Elecrow-RD/CrowPanel-ESP32-3.7-E-paper-HMI-Display-with-240-416/factory_sourecode/3.7_tow/pic/IRAD_UI_3_7/IRAD_UI_3_7_参数介绍.bmp

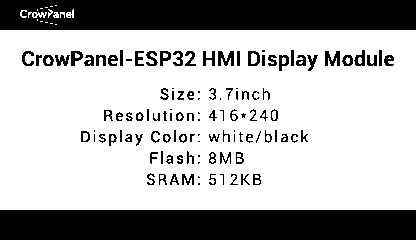
factory_sourecode/3.7_tow/pic/IRAD_UI_3_7/IRAD_UI_3_7_参数介绍.bmp
