Elecrow-RD/CrowPanel-ESP32-3.7-E-paper-HMI-Display-with-240-416/factory_sourecode/3.7_tow/pic/IRAD_UI_3_7_场景展示.bmp

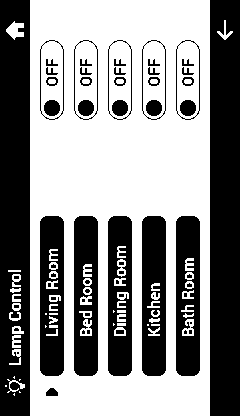
factory_sourecode/3.7_tow/pic/IRAD_UI_3_7_场景展示.bmp
