Elecrow-RD/CrowPanel-ESP32-3.7-E-paper-HMI-Display-with-240-416/factory_sourecode/3.7_tow/pic/NEW_UI_3-7_BW/NEW_UI_3-7_BW_img-05.bmp

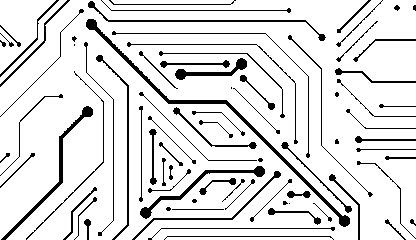
factory_sourecode/3.7_tow/pic/NEW_UI_3-7_BW/NEW_UI_3-7_BW_img-05.bmp
