Elecrow-RD/CrowPanel-ESP32-3.7-E-paper-HMI-Display-with-240-416/factory_sourecode/3.7_tow/main/pic_image.h

const unsigned char gImage_image[12480] = { /* 0X01,0X01,0XF0,0X00,0XA0,0X01, */
0X00,0X00,0X00,0X00,0X00,0X00,0X00,0X00,0X00,0X00,0X00,0X00,0X00,0X00,0X00,0X00,
0X00,0X00,0X01,0XC0,0X00,0X00,0X00,0X00,0X00,0X00,0X00,0X00,0X00,0X00,0X00,0X03,
0XC0,0X00,0X00,0X00,0X00,0X00,0X00,0X00,0X00,0X03,0X80,0X00,0X00,0X00,0X00,0X00,
0X00,0X00,0X00,0X00,0X00,0X00,0X00,0X00,0X00,0X00,0X00,0X00,0X00,0X00,0X00,0X00,
0X00,0X00,0X00,0X00,0X00,0X00,0X01,0XC0,0X00,0X00,0X00,0X00,0X00,0X00,0X00,0X00,
0X00,0X00,0X00,0X07,0X80,0X00,0X00,0X00,0X00,0X00,0X00,0X00,0X00,0X03,0X80,0X00,
0X00,0X00,0X00,0X00,0X00,0X00,0X00,0X00,0X00,0X00,0X00,0X00,0X00,0X00,0X00,0X00,
0X00,0X00,0X00,0X00,0X00,0X00,0X00,0X00,0X3F,0XFF,0XC1,0XC0,0X00,0X00,0X00,0X00,
0X00,0X00,0X00,0X00,0X00,0X00,0X00,0X0F,0X00,0X00,0X00,0X00,0X00,0X00,0X00,0X00,
0X00,0X03,0X80,0X00,0X00,0X00,0X00,0X00,0X00,0X00,0X00,0X00,0X00,0X00,0X00,0X00,
0X00,0X00,0X00,0X00,0X00,0X00,0X00,0X00,0X00,0X00,0X00,0X03,0XFF,0XFF,0XF9,0XC0,
0X00,0X00,0X00,0X00,0X00,0X00,0X00,0X00,0X00,0X00,0X00,0X1E,0X00,0X00,0X00,0X00,
0X00,0X00,0X00,0X00,0X00,0X07,0X00,0X00,0X00,0X00,0X00,0X00,0X00,0X00,0X00,0X00,
0X00,0X00,0X00,0X00,0X00,0X00,0X00,0X00,0X00,0X00,0X00,0X00,0X00,0X00,0X00,0X1F,
0XF0,0X03,0XFF,0XC0,0X00,0X00,0X00,0X00,0X00,0X00,0X00,0X00,0X00,0X00,0X00,0X3C,
0X00,0X00,0X00,0X00,0X00,0X00,0X00,0X00,0X00,0X07,0X00,0X00,0X00,0X00,0X00,0X00,
0X00,0X00,0X00,0X00,0X00,0X00,0X00,0X00,0X00,0X00,0X00,0X00,0X00,0X00,0X00,0X00,
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
0X00,0X00,0X7F,0XFF,0XF0,0X00,0X00,0X07,0X7F,0XFF,0XC0,0X00,0X3F,0XFF,0XC0,0X00,
0X00,0X3F,0XFF,0XC0,0X00,0X00,0X01,0XFF,0XF8,0X01,0XFF,0XFF,0XFF,0XFF,0X80,0X1F,
0XFF,0XE0,0X0F,0XFF,0X00,0X3F,0XFF,0XE0,0X01,0XFF,0XFF,0X00,0X07,0XFF,0XFF,0XC0,
0X00,0X3F,0XFF,0XE0,0X00,0X01,0XFF,0XFF,0XC0,0X00,0X00,0X1F,0XFF,0XFF,0X00,0X00,
0XFF,0XFF,0X80,0X00,0X00,0XFF,0XFF,0X00,0X00,0X00,0X07,0XFF,0XF0,0X00,0X7F,0XFF,
0XFF,0XFE,0X00,0X3F,0XFF,0X80,0X3F,0XFC,0X01,0XFF,0XFF,0XC0,0X07,0XFF,0XFE,0X00,
0X0F,0XFF,0XFF,0X00,0X00,0X7F,0XFF,0XC0,0X00,0X03,0XFF,0XFF,0X00,0X00,0X00,0X7F,
};
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
